Makerfabs/Project_Touch-Screen-Camera/example/SD2TFT/sd_pic/3.bmp

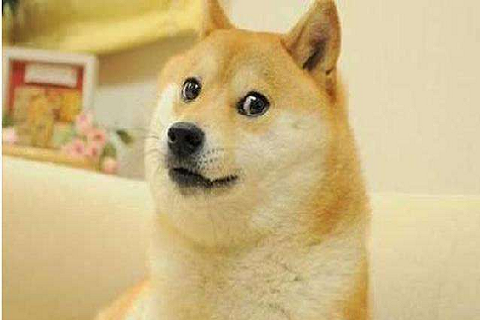
example/SD2TFT/sd_pic/3.bmp
