Makerfabs/Project_Touch-Screen-Camera/example/SD2TFT/sd_pic/4.bmp

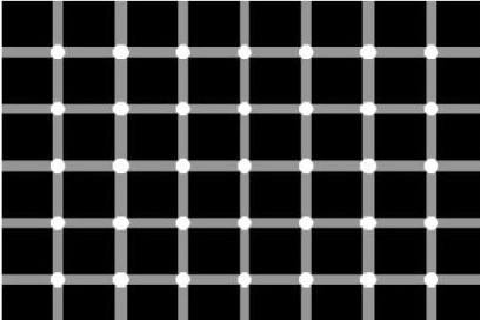
example/SD2TFT/sd_pic/4.bmp
