Makerfabs/Project_Touch-Screen-Camera/md_pic/draw.jpg

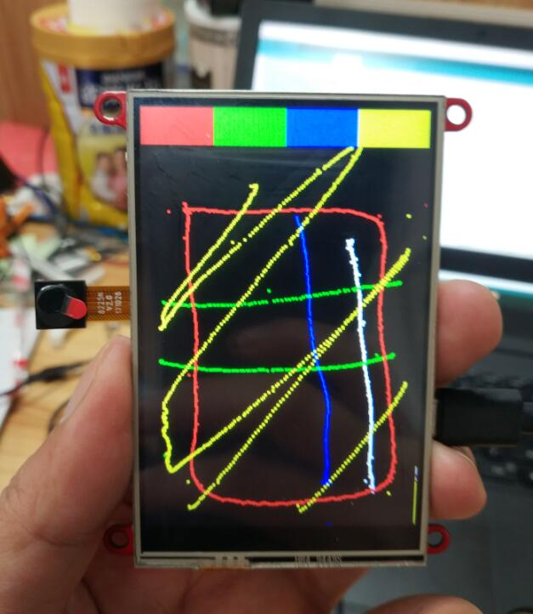
md_pic/draw.jpg
